the-tech-wiz/dtap-team-4/hardware/cad/stl/Eye R.stl

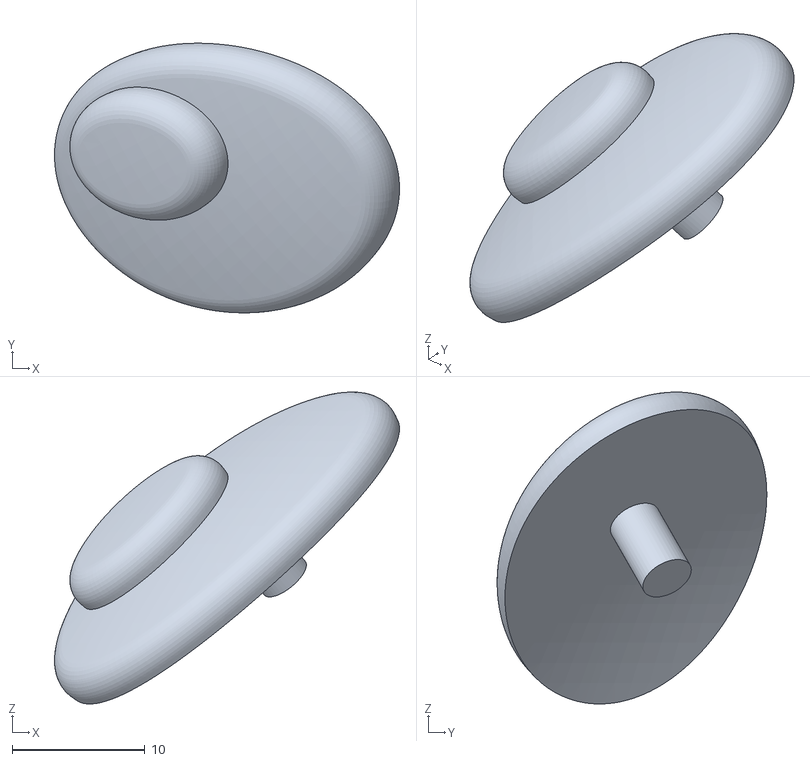
[picture p16: CAD file, 2026-05-19]
hardware/cad/stl/Eye R.stl
26.0 x 20.3 x 23.5
