the-tech-wiz/dtap-team-4/hardware/cad/stl/Nose Rabbit (Pink).stl

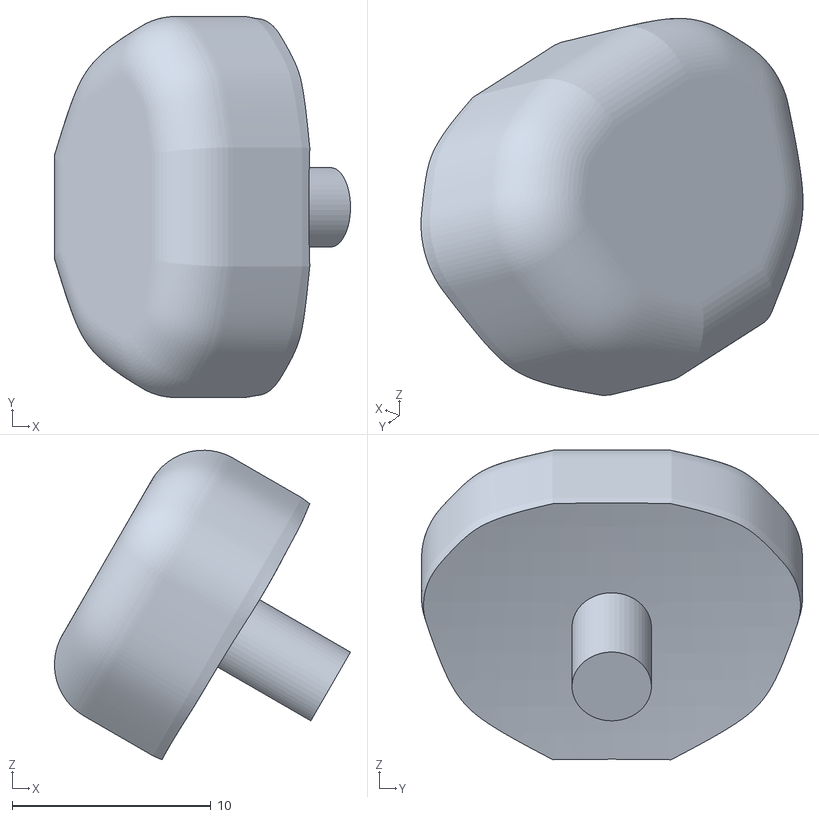
[picture p17: CAD file, 2026-05-19]
hardware/cad/stl/Nose Rabbit (Pink).stl
14.9 x 19.2 x 15.6
