the-tech-wiz/dtap-team-4/hardware/cad/stl/Tail Cat.stl

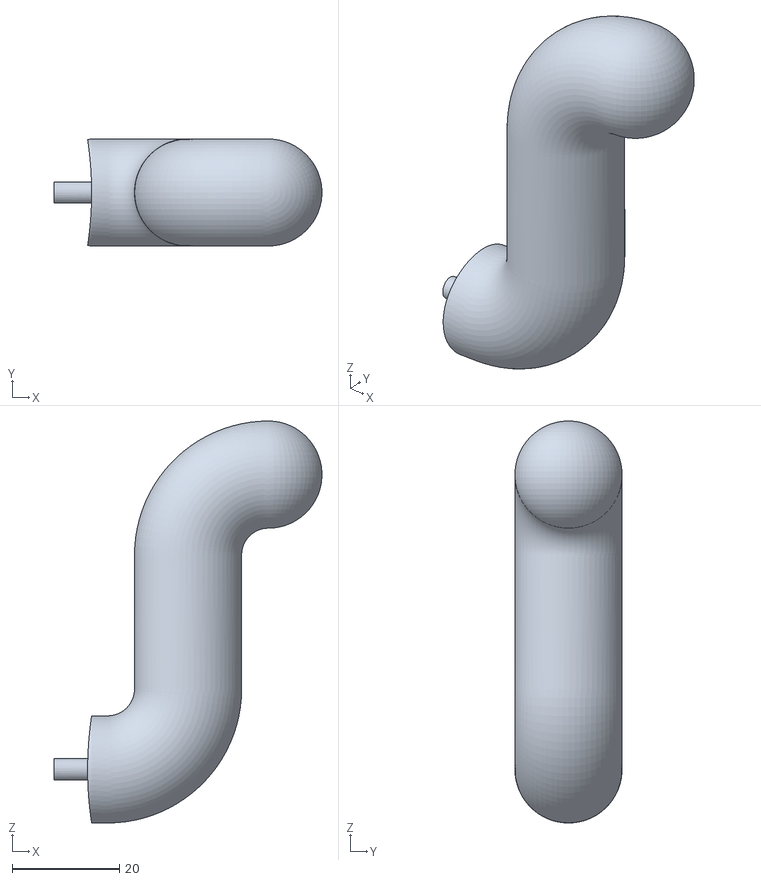
[picture p18: CAD file, 2026-05-19]
hardware/cad/stl/Tail Cat.stl
50.0 x 20.0 x 75.0
