the-tech-wiz/dtap-team-4/hardware/cad/stl/Nose Cat (Black).stl

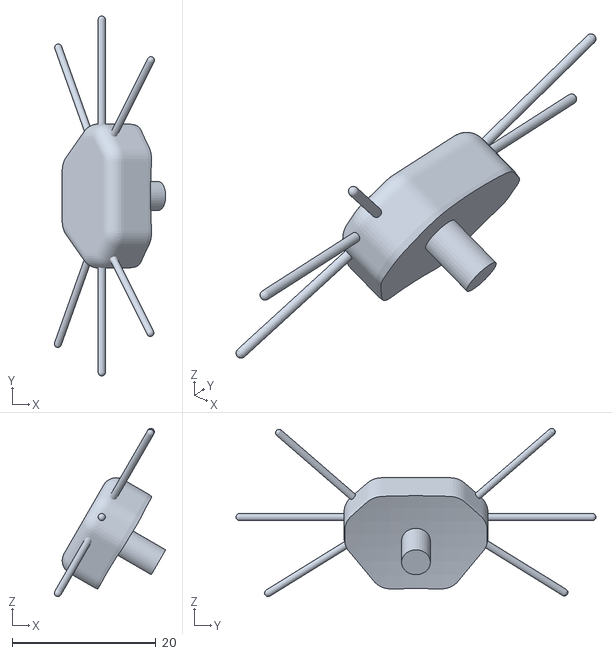
[picture p19: CAD file, 2026-05-19]
hardware/cad/stl/Nose Cat (Black).stl
15.5 x 50.0 x 23.4
