the-tech-wiz/dtap-team-4/hardware/cad/stl/Ear Rabbit.stl

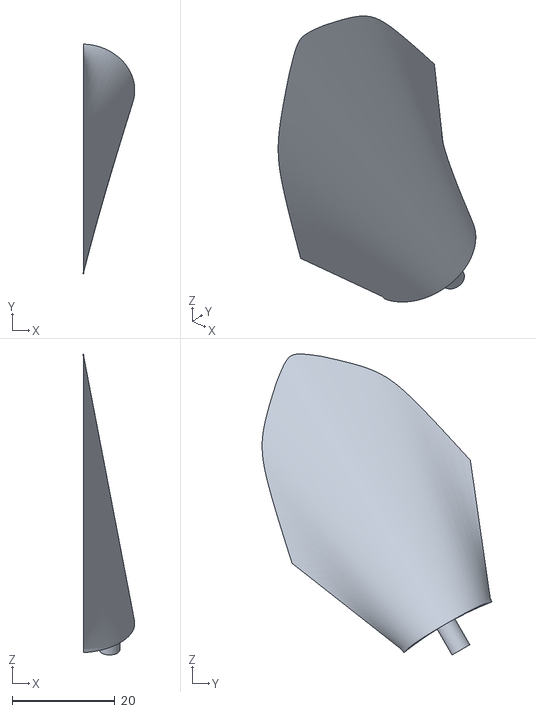
[picture p20: CAD file, 2026-05-19]
hardware/cad/stl/Ear Rabbit.stl
9.99 x 44.6 x 58.5
